4x1md/vx8_gps/docs/GY-NEO6MV2.jpg

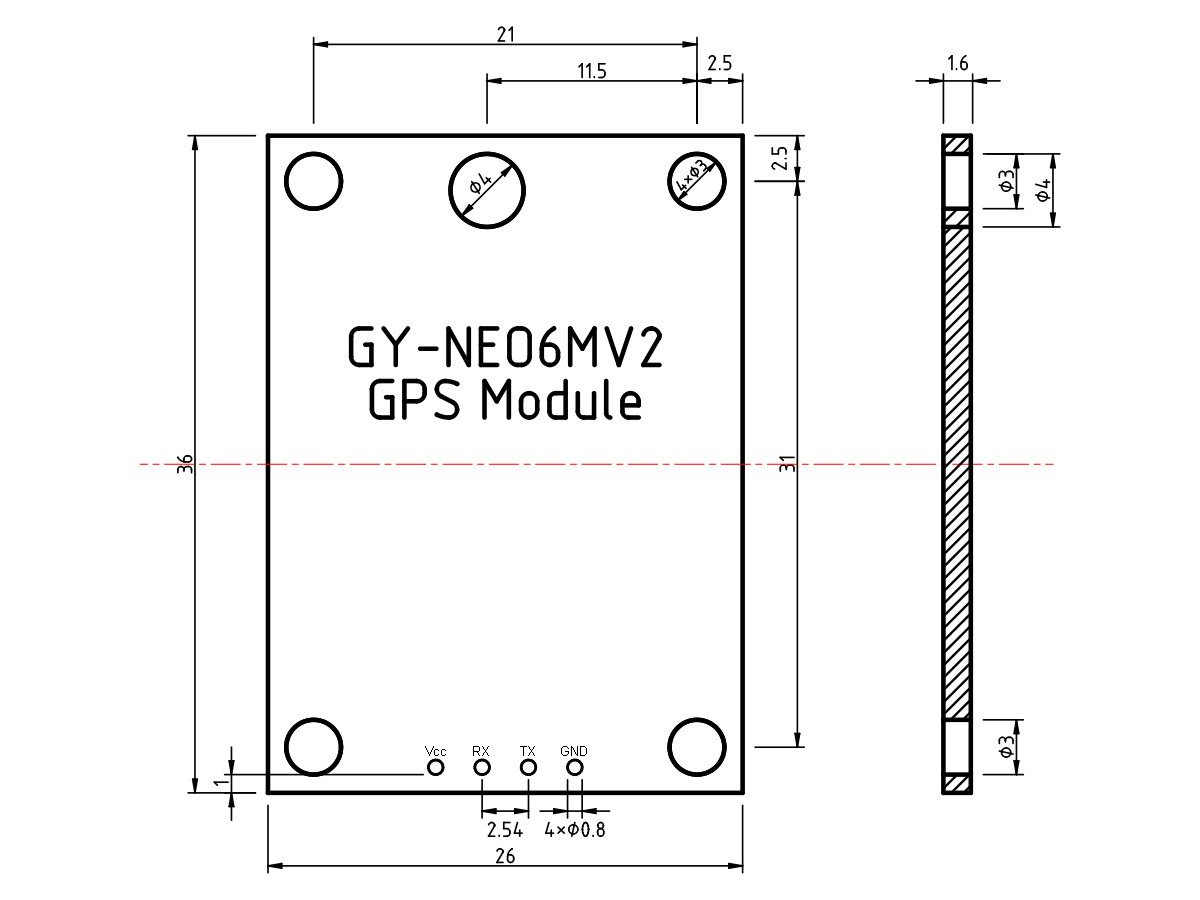
docs/GY-NEO6MV2.jpg
